mlab-modules/RP2040v01/doc/gen/dxf/RP2040v01-B_Courtyard.dxf

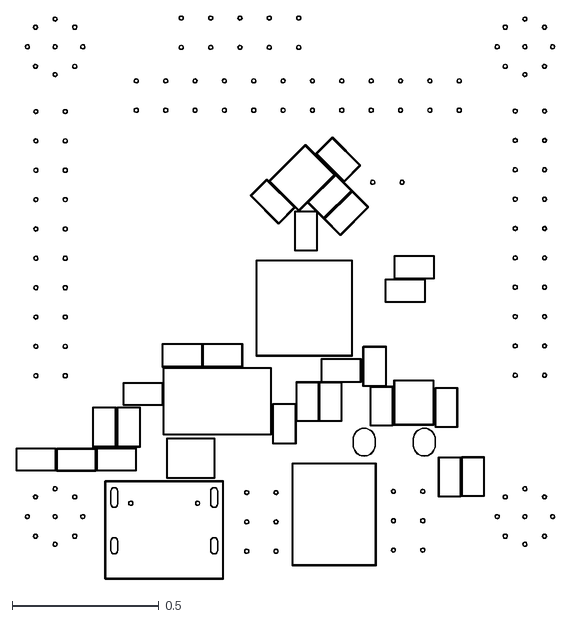
[picture p16: CAD file, 2026-02-22]
doc/gen/dxf/RP2040v01-B_Courtyard.dxf
1.83 x 1.92
