mlab-modules/RP2040v01/doc/gen/dxf/RP2040v01-Edge_Cuts.dxf

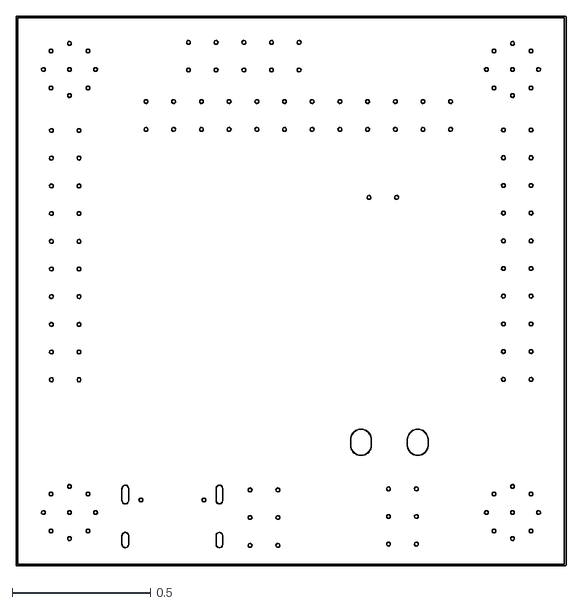
[picture p17: CAD file, 2026-02-22]
doc/gen/dxf/RP2040v01-Edge_Cuts.dxf
1.99 x 1.99
